LongHairedHacker/AS5043-Encoder/photos/boardsv12.jpg

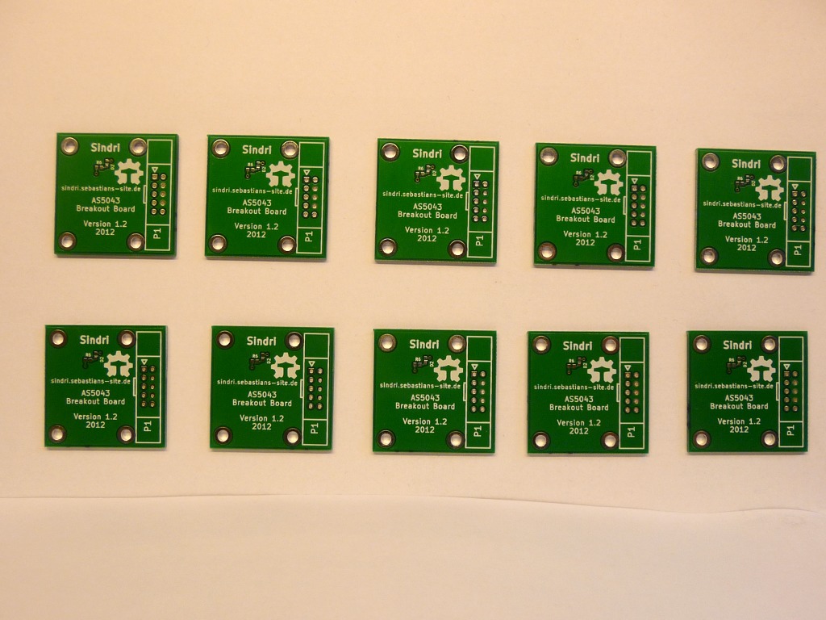
photos/boardsv12.jpg
