LongHairedHacker/AS5043-Encoder/photos/boardv12_top.jpg

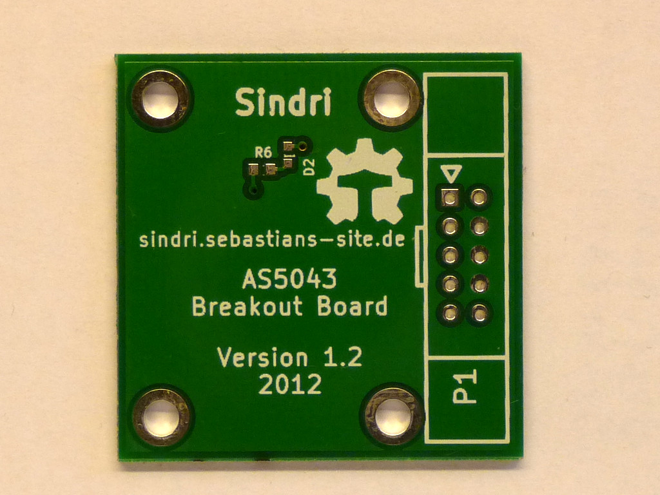
photos/boardv12_top.jpg
