LongHairedHacker/AS5043-Encoder/photos/magnets.jpg

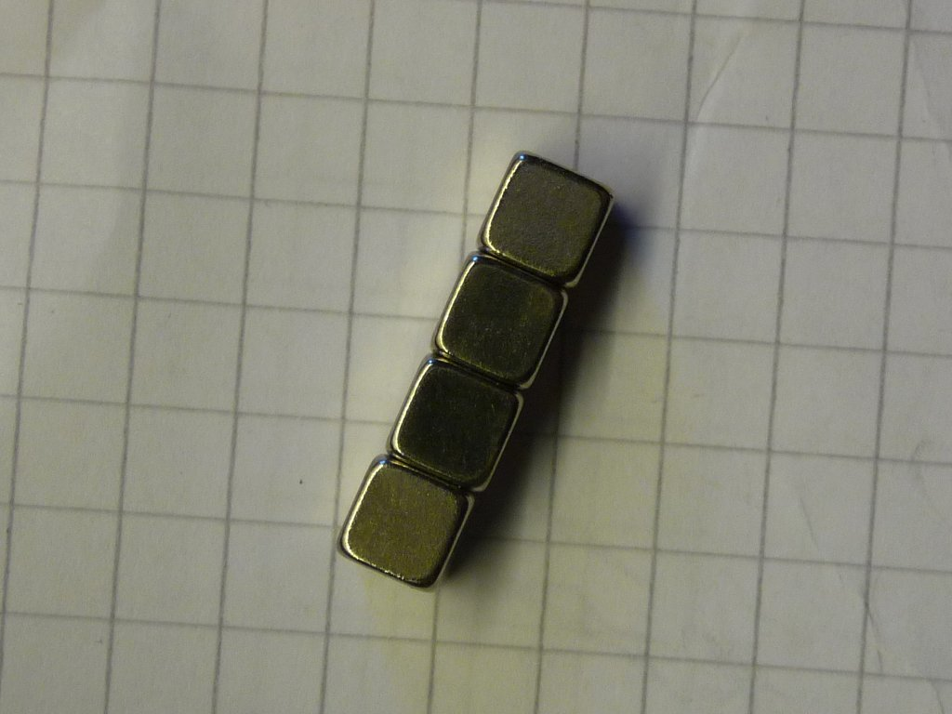
photos/magnets.jpg
