LongHairedHacker/AS5043-Encoder/photos/sensorboard_final2.jpg

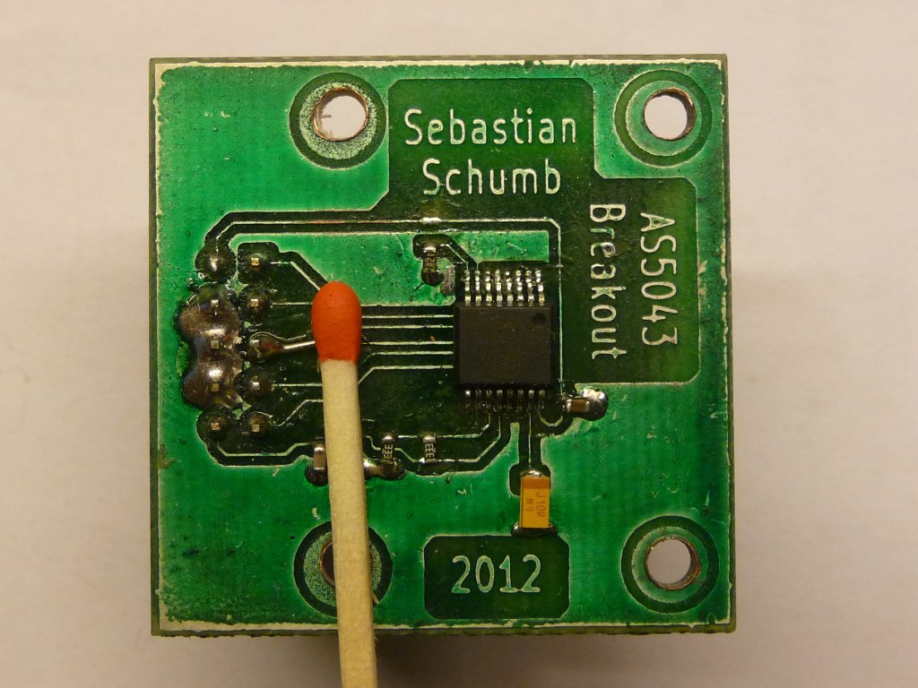
photos/sensorboard_final2.jpg
