LongHairedHacker/AS5043-Encoder/photos/sensorboard_final3.jpg

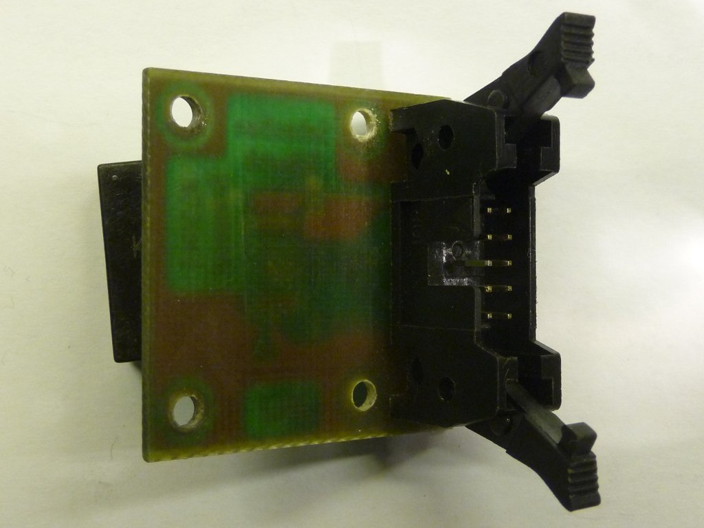
photos/sensorboard_final3.jpg
