LongHairedHacker/AS5043-Encoder/photos/sensorboard_final4.jpg

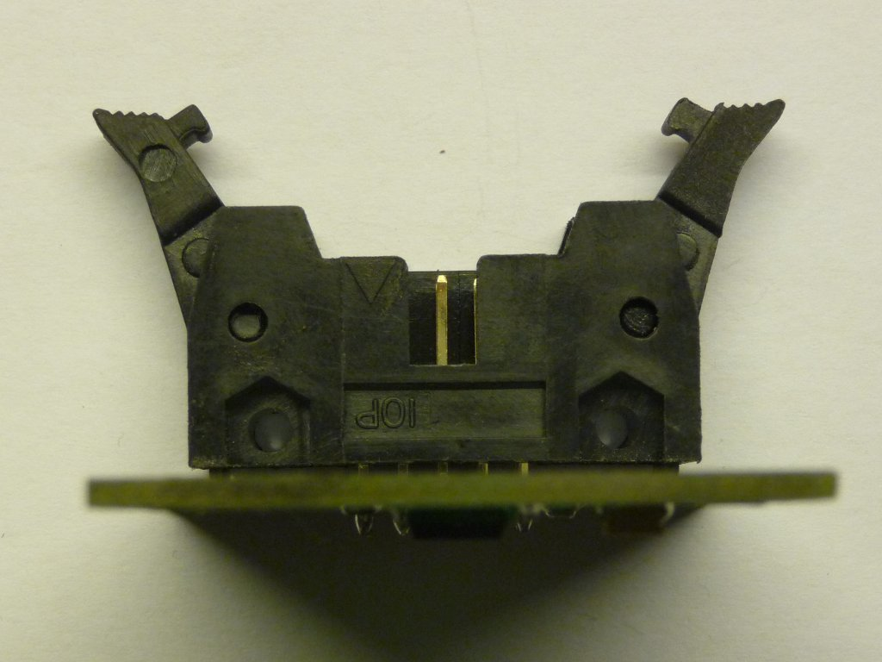
photos/sensorboard_final4.jpg
