LongHairedHacker/AS5043-Encoder/photos/sensorboard_final5.jpg

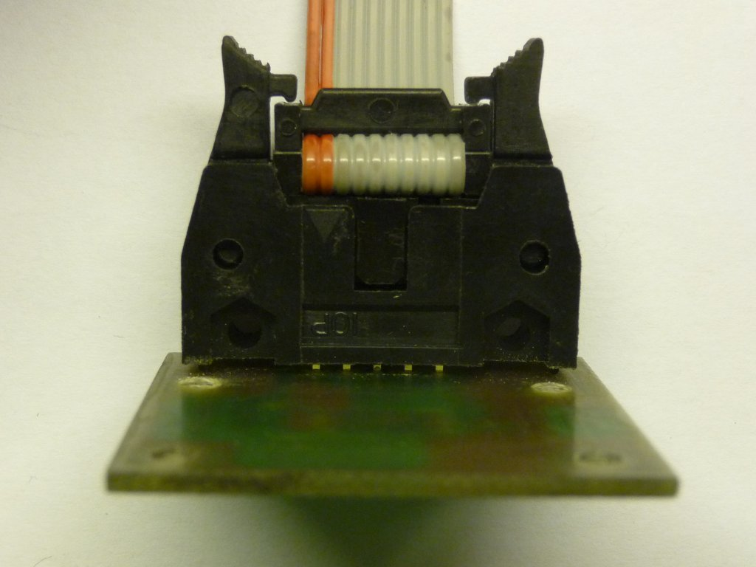
photos/sensorboard_final5.jpg
