LongHairedHacker/AS5043-Encoder/photos/sensorboard_greencoat2.jpg

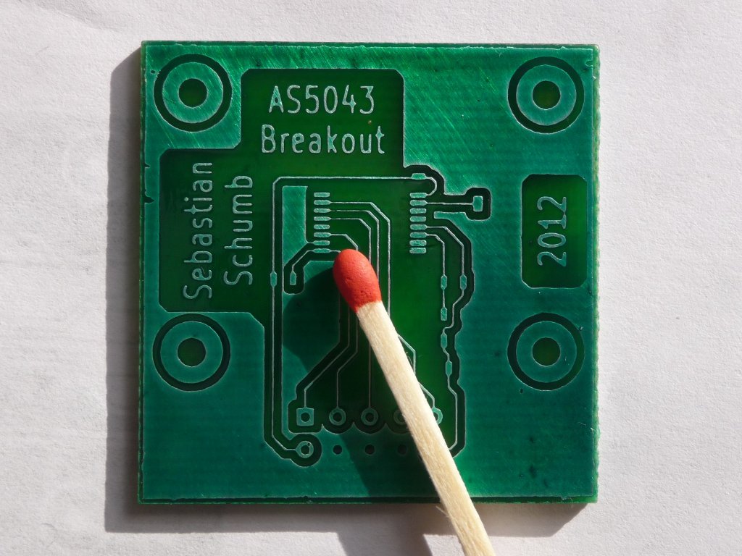
photos/sensorboard_greencoat2.jpg
