LongHairedHacker/AS5043-Encoder/photos/sensorboard_tin1.jpg

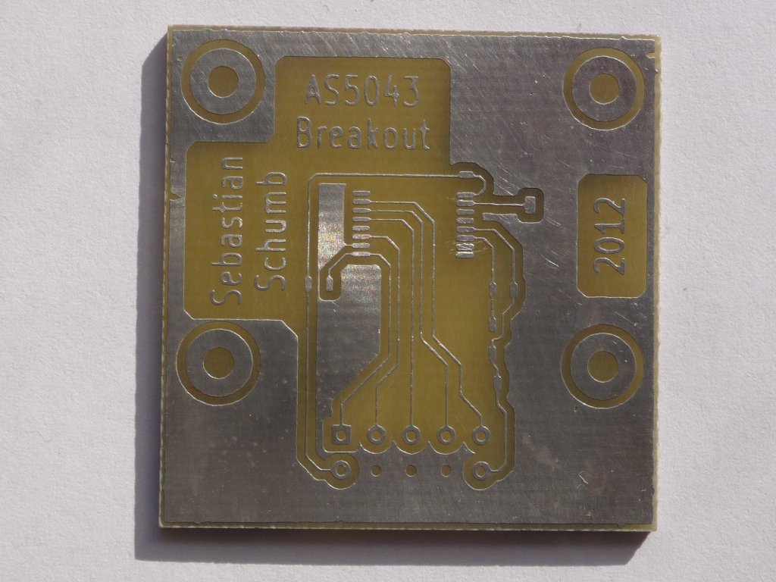
photos/sensorboard_tin1.jpg
