LongHairedHacker/AS5043-Encoder/photos/shaft1.jpg

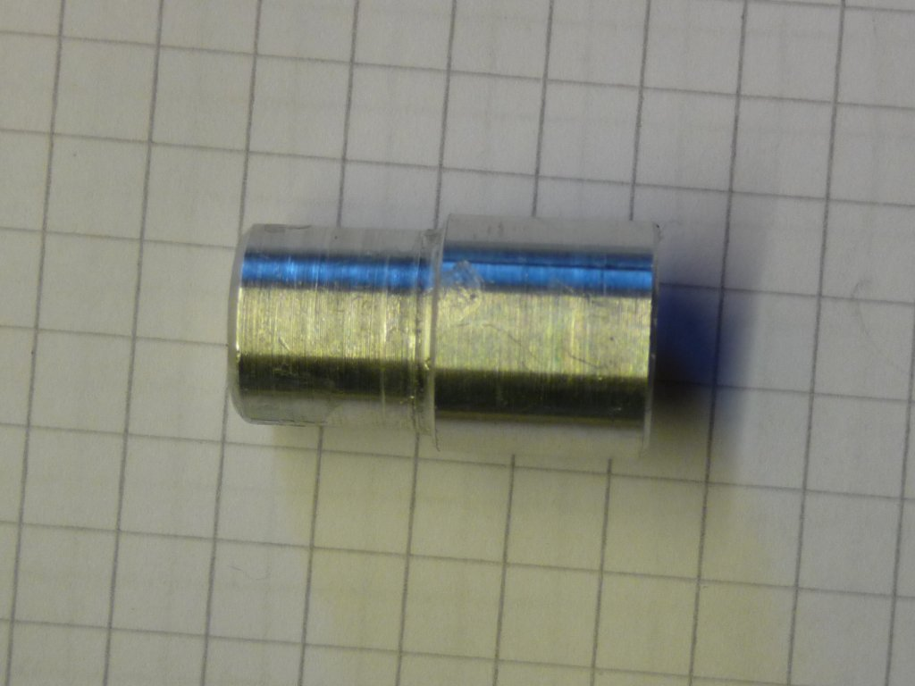
photos/shaft1.jpg
