LongHairedHacker/AS5043-Encoder/photos/shaft2.jpg

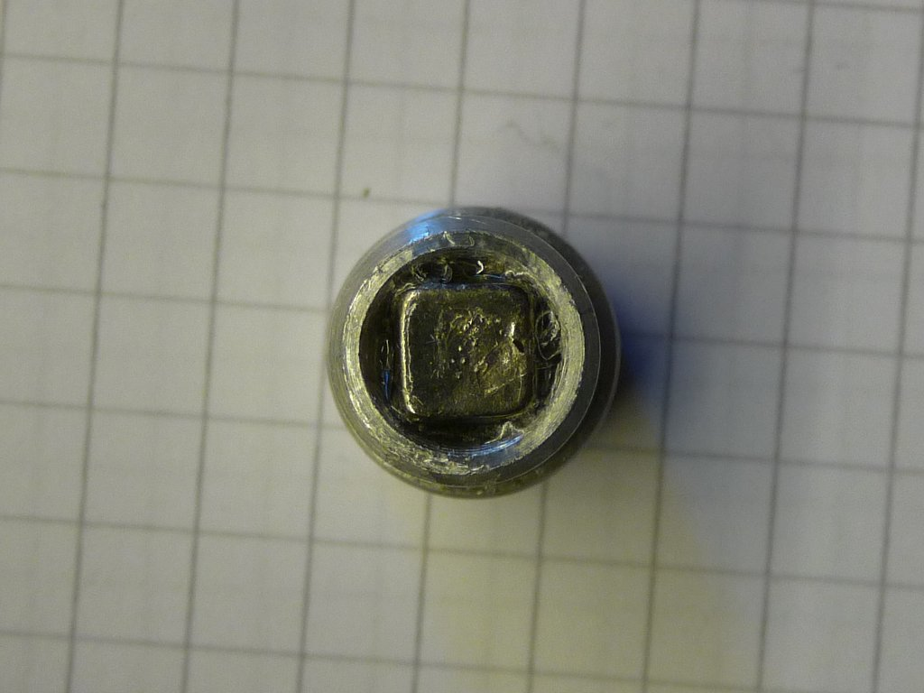
photos/shaft2.jpg
