LongHairedHacker/AS5043-Encoder/photos/shaft3.jpg

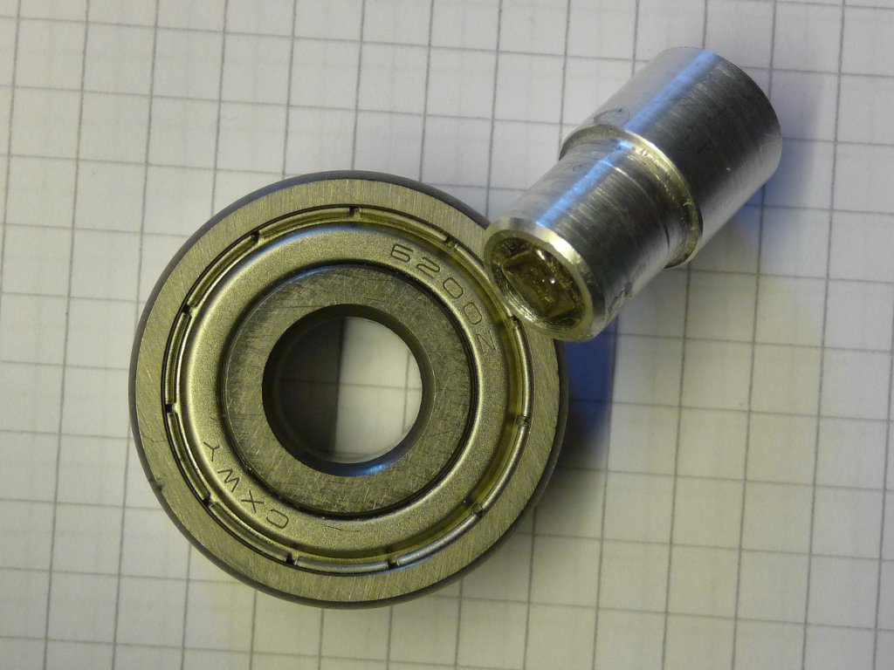
photos/shaft3.jpg
