LongHairedHacker/AS5043-Encoder/photos/shaft4.jpg

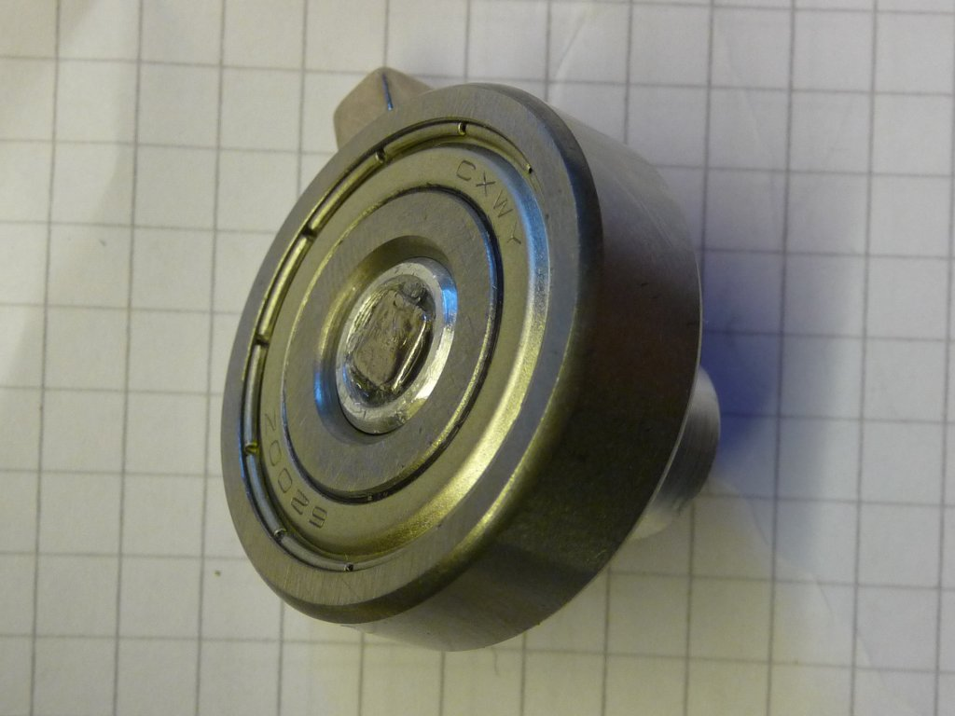
photos/shaft4.jpg
