LongHairedHacker/AS5043-Encoder/photos/assembled1.jpg

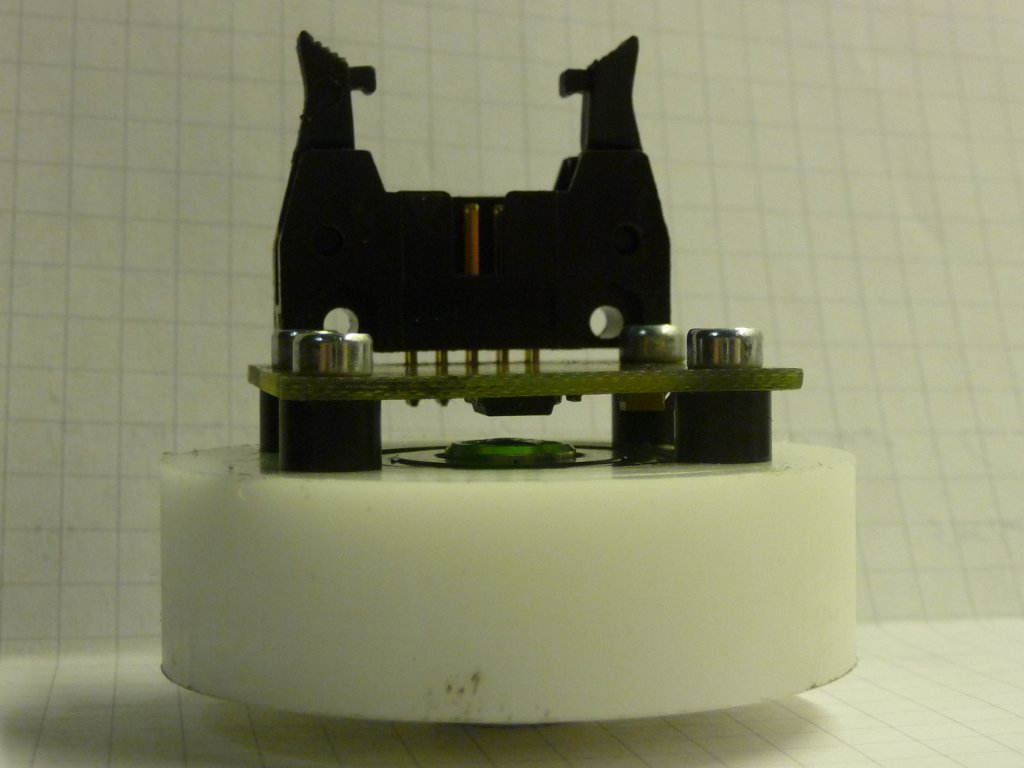
photos/assembled1.jpg
