LongHairedHacker/AS5043-Encoder/photos/assembled3.jpg

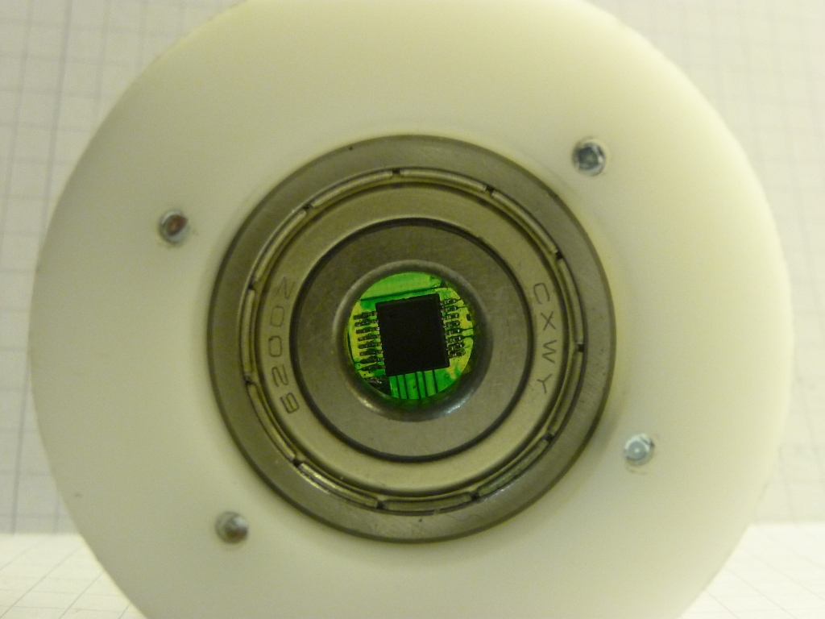
photos/assembled3.jpg
